TactileVision/CollabJam-PCB/v4/project_libs/3d_models/LTST-S220KFKT.stp

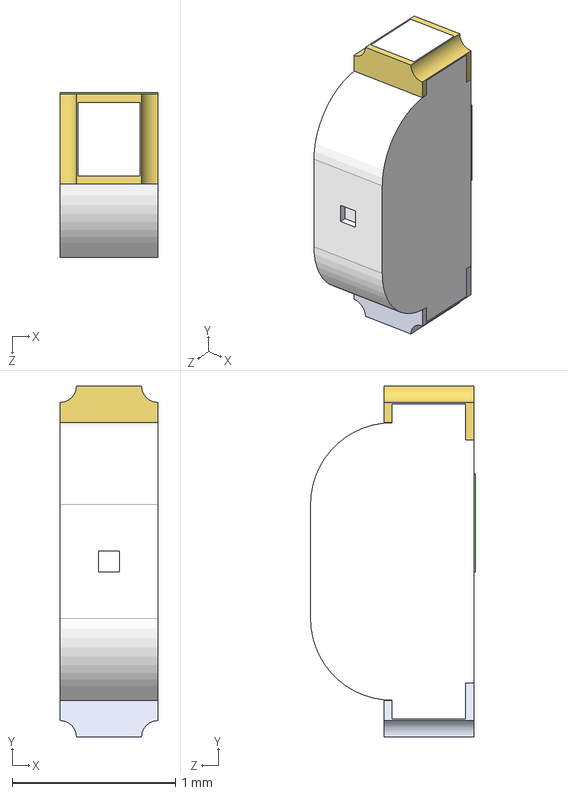
[picture p15: CAD file, 2023-05-02]
v4/project_libs/3d_models/LTST-S220KFKT.stp
0.6 x 2.15 x 1.01 mm
