TactileVision/CollabJam-PCB/v4/project_libs/3d_models/SSAJ110100.stp

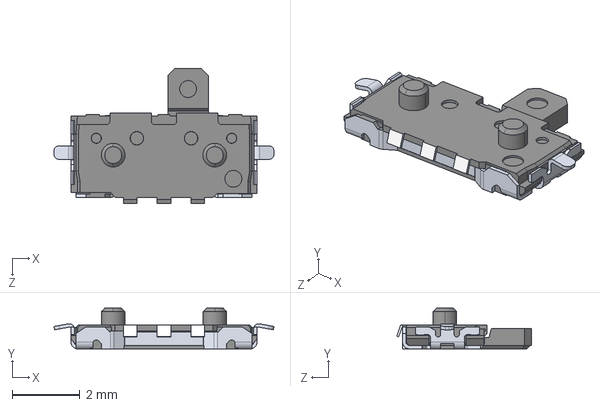
[picture p16: CAD file, 2023-05-02]
v4/project_libs/3d_models/SSAJ110100.stp
6.50 x 1.20 x 3.98 mm
