TactileVision/CollabJam-PCB/v4/project_libs/3d_models/SIP32510DT-T1-GE3.stp

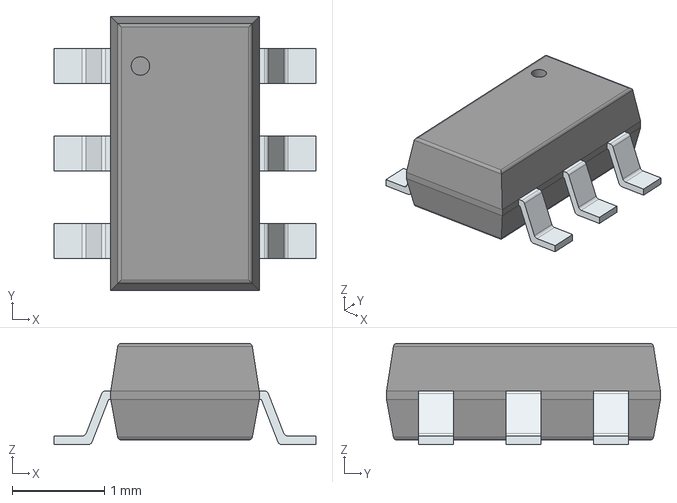
[picture p17: CAD file, 2023-07-28]
v4/project_libs/3d_models/SIP32510DT-T1-GE3.stp
2.84 x 2.98 x 1.10 mm
PinsArrayLR
