TactileVision/CollabJam-PCB/v4/project_libs/3d_models/450404015514.stp

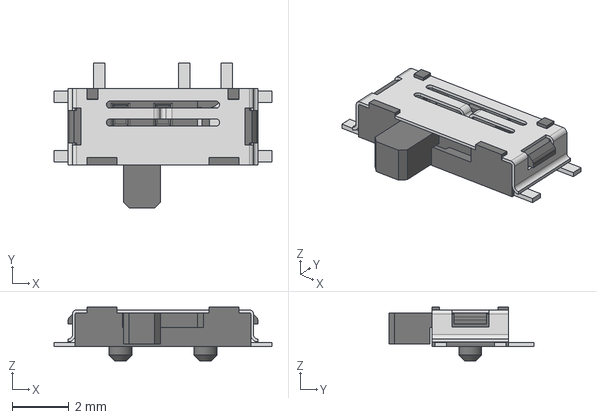
[picture p18: CAD file, 2023-07-28]
v4/project_libs/3d_models/450404015514.stp
7.70 x 5.13 x 1.90 mm
